beau-seidon/TinyMIDI2CV/hardware/TinyMIDI2CV.kicad_sch

## KiCad design hardware/TinyMIDI2CV.kicad_sch (2024-09-18)

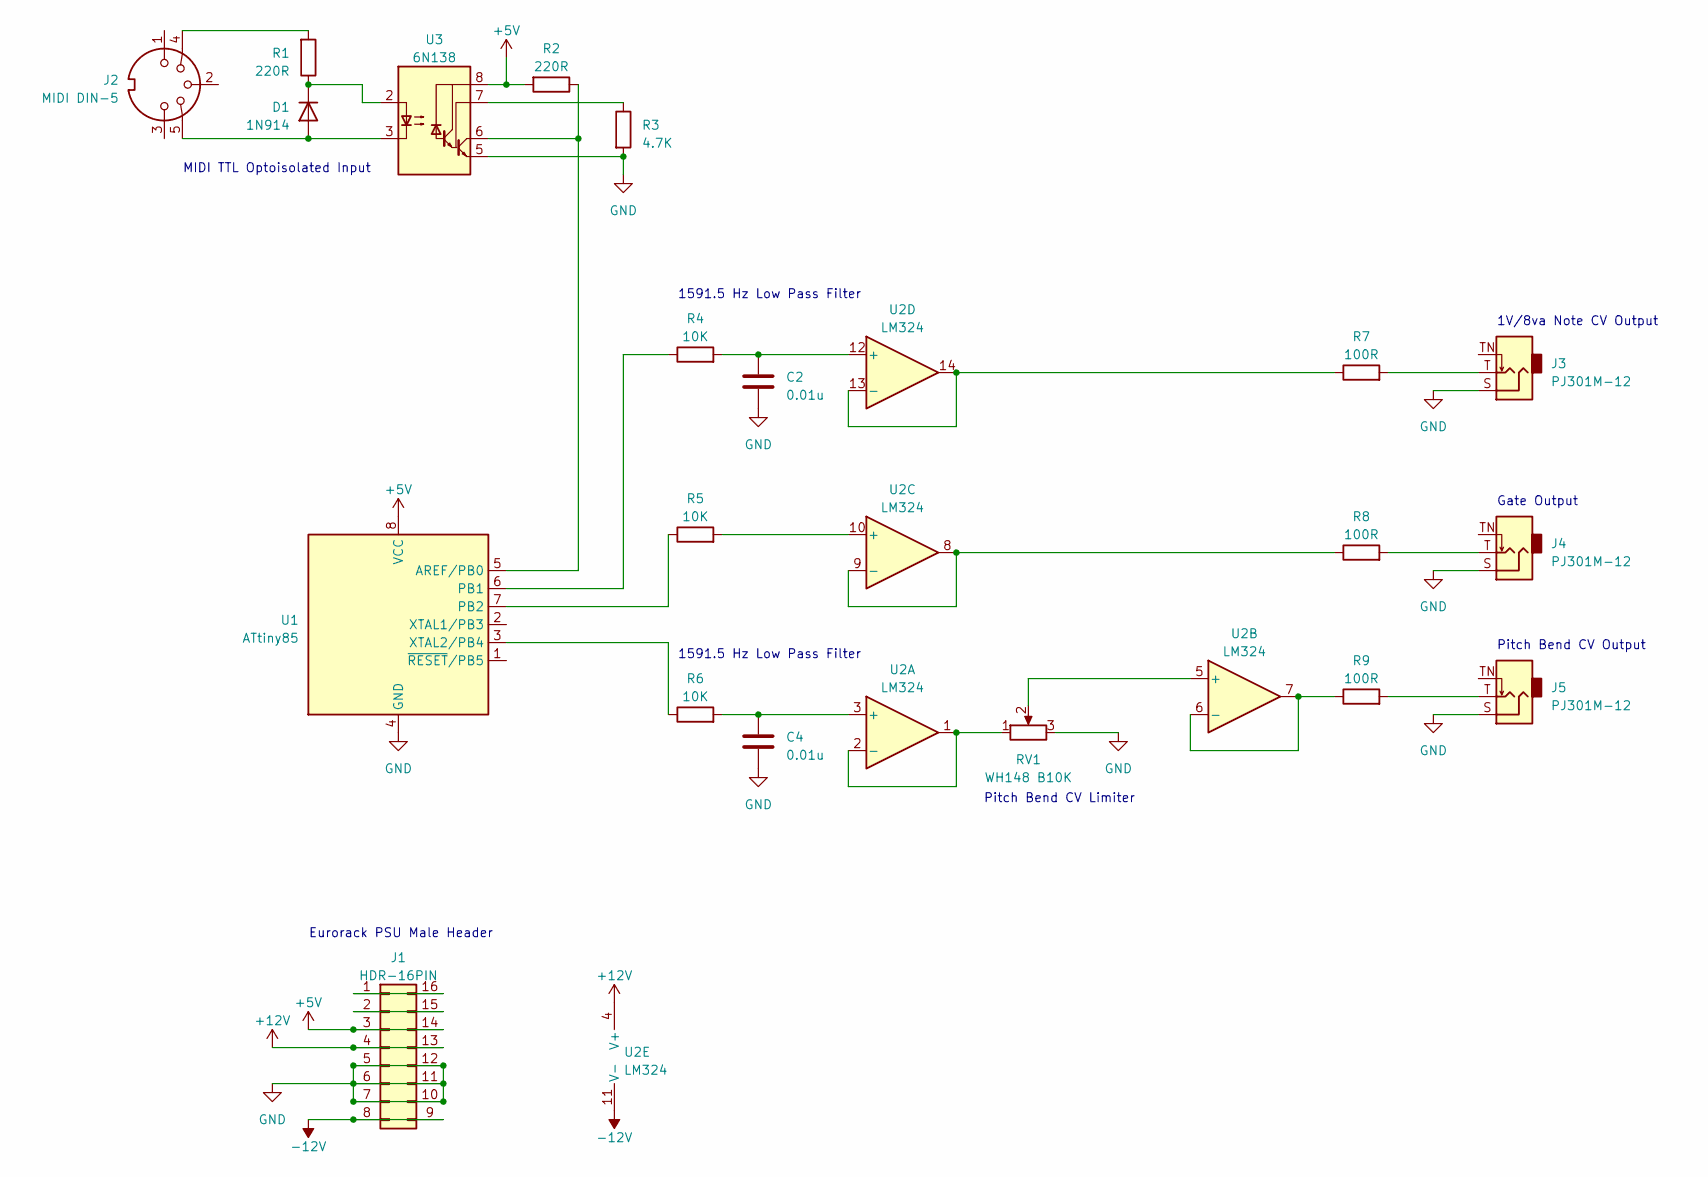
[picture p4: schematic TinyMIDI2CV.kicad_sch]

Parts:
C2, C4: 0.01u; C_Disc_D5.0mm_W2.5mm_P2.50mm
D1: 1N914; D_DO-35_SOD27_P7.62mm_Horizontal
J1: HDR-16PIN
J2: MIDI DIN-5
J3, J4, J5: PJ301M-12
R1, R2: 220R; R_Axial_DIN0207_L6.3mm_D2.5mm_P5.08mm_Vertical
R3: 4.7K; R_Axial_DIN0207_L6.3mm_D2.5mm_P5.08mm_Vertical
R4, R5, R6: 10K; R_Axial_DIN0207_L6.3mm_D2.5mm_P5.08mm_Vertical
R7, R8, R9: 100R; R_Axial_DIN0207_L6.3mm_D2.5mm_P5.08mm_Vertical
RV1: WH148 B10K
U1: ATtiny85; DIP-8_W7.62mm
U2: LM324; DIP-14_W7.62mm_Socket_LongPads
U3: 6N138

Connections:
+5V: J1.3, J1.14, R2.2, U1.8 (VCC), U3.8 (VCC)
+12V: J1.4, J1.13, U2.4 (V+)
-12V: J1.8, J1.9, U2.11 (V-)
GND: C2.1, C4.1, J1.5, J1.6, J1.7, J1.10, J1.11, J1.12, J3.S, J4.S, J5.S, R3.2, RV1.3, U1.4 (GND), U3.5 (GND)
unnamed: C2.2, R4.2, U2.12 (+)
unnamed: C4.2, R6.2, U2.3 (+)
unnamed: D1.1 (K), R1.1, U3.2 (C1)
unnamed: D1.2 (A), J2.5, U3.3 (C2)
unnamed: J1.1, J1.16
unnamed: J1.2, J1.15
unnamed: J2.4, R1.2
unnamed: J3.T, R7.2
unnamed: J4.T, R8.2
unnamed: J5.T, R9.2
unnamed: R2.1, U1.5 (AREF/PB0), U3.6 (VO2)
unnamed: R3.1, U3.7 (VO1)
unnamed: R4.1, U1.6 (PB1)
unnamed: R5.1, U1.7 (PB2)
unnamed: R5.2, U2.10 (+)
unnamed: R6.1, U1.3 (XTAL2/PB4)
unnamed: R7.1, U2.13 (-), U2.14
unnamed: R8.1, U2.8, U2.9 (-)
unnamed: R9.1, U2.6 (-), U2.7
unnamed: RV1.1, U2.1, U2.2 (-)
unnamed: RV1.2, U2.5 (+)

Notes on the sheet:
Eurorack PSU Male Header
1591.5 Hz Low Pass Filter
1V/8va Note CV Output
Pitch Bend CV Limiter
Gate Output
Pitch Bend CV Output
MIDI TTL Optoisolated Input
